sidhb23/Alfond-Data-Logger/Testing.ioc

Mcu.UserName=STM32U545RETxQ
PA0.Signal=UART4_TX
PA5.Signal=GPIO_Output
PA7.Signal=USART3_TX
PB10.Signal=I2C2_SCL
PB14.Signal=I2C2_SDA
PB6.Signal=I2C1_SCL
PC0.Signal=I2C3_SCL
PC1.Signal=I2C3_SDA
PC12.Signal=UART5_TX
PC13.Signal=GPXTI13
PD2.Signal=UART5_RX
